tenderlove/tendair/firmware/main/sensirion_i2c_hal.c

/*
 * Copyright (c) 2023, Sensirion AG
 * All rights reserved.
 *
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
 * * Neither the name of Sensirion AG nor the names of its
 *   contributors may be used to endorse or promote products derived from
 *   this software without specific prior written permission.
 *
 * THIS SOFTWARE IS PROVIDED BY THE COPYRIGHT HOLDERS AND CONTRIBUTORS "AS IS"
 * AND ANY EXPRESS OR IMPLIED WARRANTIES, INCLUDING, BUT NOT LIMITED TO, THE
 * IMPLIED WARRANTIES OF MERCHANTABILITY AND FITNESS FOR A PARTICULAR PURPOSE
 * ARE DISCLAIMED. IN NO EVENT SHALL THE COPYRIGHT HOLDER OR CONTRIBUTORS BE
 * LIABLE FOR ANY DIRECT, INDIRECT, INCIDENTAL, SPECIAL, EXEMPLARY, OR
 * CONSEQUENTIAL DAMAGES (INCLUDING, BUT NOT LIMITED TO, PROCUREMENT OF
 * SUBSTITUTE GOODS OR SERVICES; LOSS OF USE, DATA, OR PROFITS; OR BUSINESS
 * INTERRUPTION) HOWEVER CAUSED AND ON ANY THEORY OF LIABILITY, WHETHER IN
 * CONTRACT, STRICT LIABILITY, OR TORT (INCLUDING NEGLIGENCE OR OTHERWISE)
 * ARISING IN ANY WAY OUT OF THE USE OF THIS SOFTWARE, EVEN IF ADVISED OF THE
 * POSSIBILITY OF SUCH DAMAGE.
 */

#include "sensirion_i2c_hal.h"
#include "sensirion_common.h"
#include "sensirion_config.h"

#include <esp_log.h>
#include <freertos/FreeRTOS.h>
#include <freertos/task.h>
#include <string.h>

#include "sensirion_i2c_esp32_config.h"

static const char* TAG = "sensirion_i2c_hal";

#define SLEEP_MS(x) \
    vTaskDelay(((x) + portTICK_PERIOD_MS - 1) / portTICK_PERIOD_MS)
#define CHECK(x)                \
    do {                        \
        esp_err_t __;           \
        if ((__ = x) != ESP_OK) \
            return __;          \
    } while (0)
#define CHECK_ARG(VAL)                  \
    do {                                \
        if (!(VAL))                     \
            return ESP_ERR_INVALID_ARG; \
    } while (0)
#define UNUSED_PARAM(x) (void)x

static i2c_master_dev_handle_t dev_handle = {0};
static struct esp32_i2c_config i2c_cfg = {0};
static esp_err_t i2c_ok = ESP_OK;

/*
 * INSTRUCTIONS
 * ============
 *
 * Implement all functions where they are marked as IMPLEMENT.
 * Follow the function specification in the comments.
 */

/**
 * Select the current i2c bus by index.
 * All following i2c operations will be directed at that bus.
 *
 * THE IMPLEMENTATION IS OPTIONAL ON SINGLE-BUS SETUPS (all sensors on the same
 * bus)
 *
 * @param bus_idx   Bus index to select
 * @returns         0 on success, an error code otherwise
 */
int16_t sensirion_i2c_hal_select_bus(uint8_t bus_idx) {
    /* TODO:IMPLEMENT or leave empty if all sensors are located on one single
     * bus
     */
    return NOT_IMPLEMENTED_ERROR;
}

esp_err_t sensirion_i2c_config_esp32(struct esp32_i2c_config* cfg) {
    if (cfg != NULL) {
        memcpy(&i2c_cfg, cfg, sizeof(*cfg));
        return ESP_OK;
    } else {
        return ESP_FAIL;
    }
}

esp_err_t sensirion_i2c_esp32_ok(void) {
    return i2c_ok;
}

/**
 * Initialize all hard- and software components that are needed for the I2C
 * communication.
 */
void sensirion_i2c_hal_init(i2c_master_bus_handle_t *bus_handle) {
    i2c_master_bus_config_t bus_config = {
        .i2c_port = I2C_MASTER_NUM,
        .sda_io_num = I2C_MASTER_SDA_IO,
        .scl_io_num = I2C_MASTER_SCL_IO,
        .clk_source = I2C_CLK_SRC_DEFAULT,
        .glitch_ignore_cnt = 7,
        .flags.enable_internal_pullup = true,
    };
    ESP_ERROR_CHECK(i2c_new_master_bus(&bus_config, bus_handle));

    i2c_device_config_t dev_config = {
        .dev_addr_length = I2C_ADDR_BIT_LEN_7,
        .device_address = SEN66_SENSOR_ADDR,
        .scl_speed_hz = I2C_MASTER_FREQ_HZ,
    };
    ESP_ERROR_CHECK(i2c_master_bus_add_device(*bus_handle, &dev_config, &dev_handle));
}

/**
 * Release all resources initialized by sensirion_i2c_hal_init().
 */
void sensirion_i2c_hal_free(void) {
}

/**
 * Execute one read transaction on the I2C bus, reading a given number of bytes.
 * If the device does not acknowledge the read command, an error shall be
 * returned.
 *
 * @param address 7-bit I2C address to read from
 * @param data    pointer to the buffer where the data is to be stored
 * @param count   number of bytes to read from I2C and store in the buffer
 * @returns 0 on success, error code otherwise
 */
int8_t sensirion_i2c_hal_read(uint8_t address, uint8_t* data, uint16_t count) {
    ESP_LOGD(TAG, "sensirion_i2c_hal_read: len: %d", count);
    ESP_ERROR_CHECK(i2c_master_receive(dev_handle, data, count, I2C_MASTER_TIMEOUT_MS));
    ESP_LOGD(TAG, "READ OK");
    return (int8_t)ESP_OK;
}

/**
 * Execute one write transaction on the I2C bus, sending a given number of
 * bytes. The bytes in the supplied buffer must be sent to the given address. If
 * the slave device does not acknowledge any of the bytes, an error shall be
 * returned.
 *
 * @param address 7-bit I2C address to write to
 * @param data    pointer to the buffer containing the data to write
 * @param count   number of bytes to read from the buffer and send over I2C
 * @returns 0 on success, error code otherwise
 */
int8_t sensirion_i2c_hal_write(uint8_t address, const uint8_t* data,
                               uint16_t count) {
    ESP_LOGD(TAG, "sensirion_i2c_hal_write: len: %d", count);
    ESP_ERROR_CHECK(i2c_master_transmit(dev_handle, data, count, I2C_MASTER_TIMEOUT_MS));
    ESP_LOGD(TAG, "WRITE OK");
    return (int8_t)ESP_OK;
}

/**
 * Sleep for a given number of microseconds. The function should delay the
 * execution for at least the given time, but may also sleep longer.
 *
 * Despite the unit, a <10 millisecond precision is sufficient.
 *
 * @param useconds the sleep time in microseconds
 */
void sensirion_i2c_hal_sleep_usec(uint32_t useconds) {
    ESP_LOGD(TAG, "sensirion_i2c_hal_sleep: %d usec", useconds);
    SLEEP_MS(useconds / 1000);
}
